PetyC/STM32H743II_PCB/1.Hardware/3D/STEP/TYPE-C-16.STEP

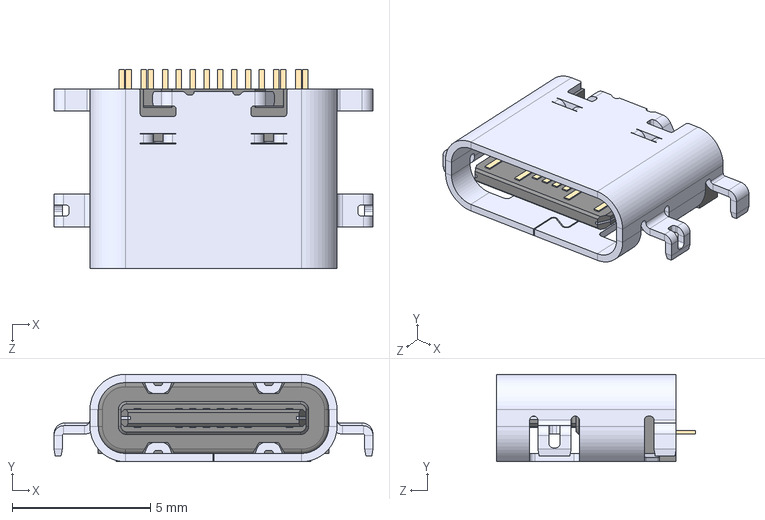
[picture p15: CAD file, 2022-04-13]
1.Hardware/3D/STEP/TYPE-C-16.STEP
11.5 x 3.16 x 7.20 mm
