PetyC/STM32H743II_PCB/1.Hardware/3D/STEP/DF40C-44DP-0.4V.STEP

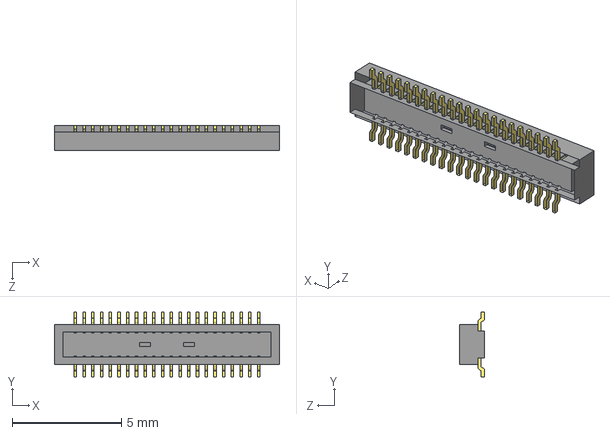
[picture p16: CAD file, 2022-04-13]
1.Hardware/3D/STEP/DF40C-44DP-0.4V.STEP
10.3 x 2.97 x 1.14 mm
