PetyC/STM32H743II_PCB/1.Hardware/3D/STEP/K3-2410S-F1.STEP

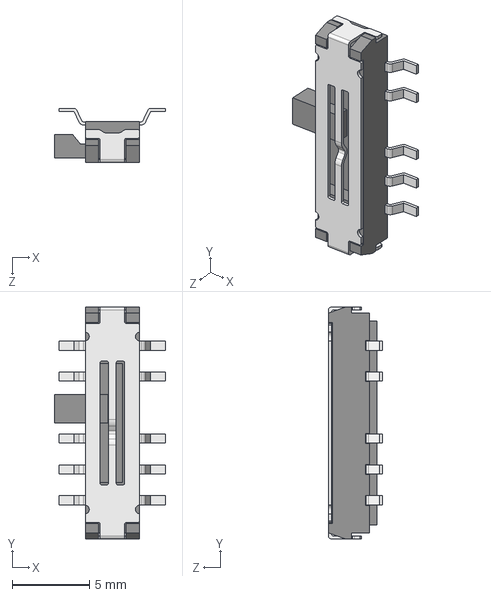
[picture p17: CAD file, 2022-04-13]
1.Hardware/3D/STEP/K3-2410S-F1.STEP
7.20 x 15.0 x 3.50 mm
