PetyC/STM32H743II_PCB/1.Hardware/3D/STEP/TM-2023.STEP

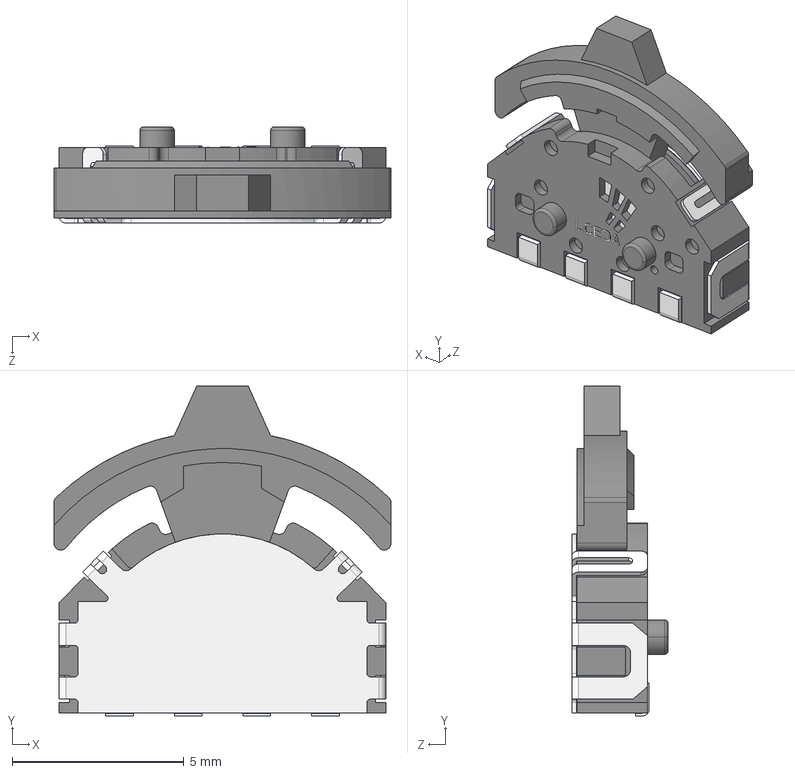
[picture p18: CAD file, 2022-04-13]
1.Hardware/3D/STEP/TM-2023.STEP
9.80 x 9.59 x 2.80 mm
